KwongKw/self-balance-reuleaux-triangle/src/test/test.ino

#include <SimpleFOC.h>

MagneticSensorI2C sensor = MagneticSensorI2C(AS5600_I2C);
TwoWire I2Ctwo = TwoWire(1);

BLDCMotor motor = BLDCMotor(7);
BLDCDriver3PWM driver = BLDCDriver3PWM(14, 12, 13, 27);

// include commander interface
Commander command = Commander(Serial);
void doMotor(char* cmd) { command.motor(&motor, cmd); }

void setup(){
  I2Ctwo.begin(17, 16, 400000);  //SDA,SCL
  sensor.init(&I2Ctwo);

  //连接motor对象与传感器对象
  motor.linkSensor(&sensor);
  
  // add the motor to the commander interface
  // The letter (here 'M') you will provide to the SimpleFOCStudio
  command.add('M',doMotor,'motor');
  // tell the motor to use the monitoring
  motor.useMonitoring(Serial);
  motor.monitor_downsample = 0; // disable monitor at first - optional
  ...

}
void loop(){
  ....

  ....
  // real-time monitoring calls
  motor.monitor();
  // real-time commander calls
  command.run();
}
